psu-epl/Capstones-LID_Tracking/doc/web_interface/Hierarchy_prelim.jpg

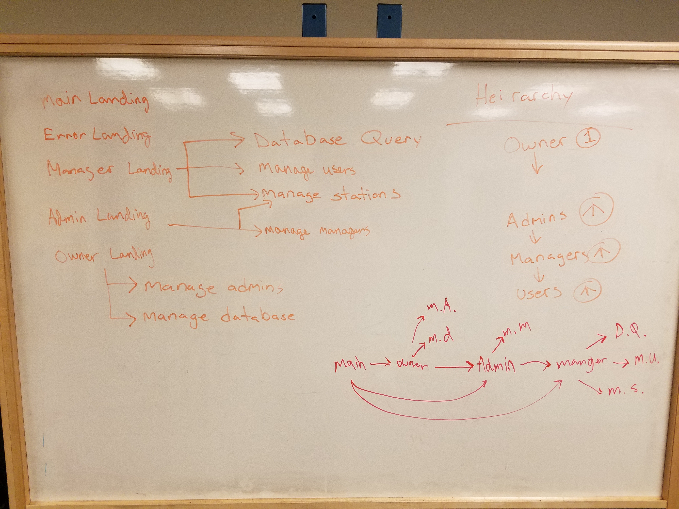
doc/web_interface/Hierarchy_prelim.jpg
