psu-epl/Capstones-LID_Tracking/doc/web_interface/State_Diagram_prelim.jpg

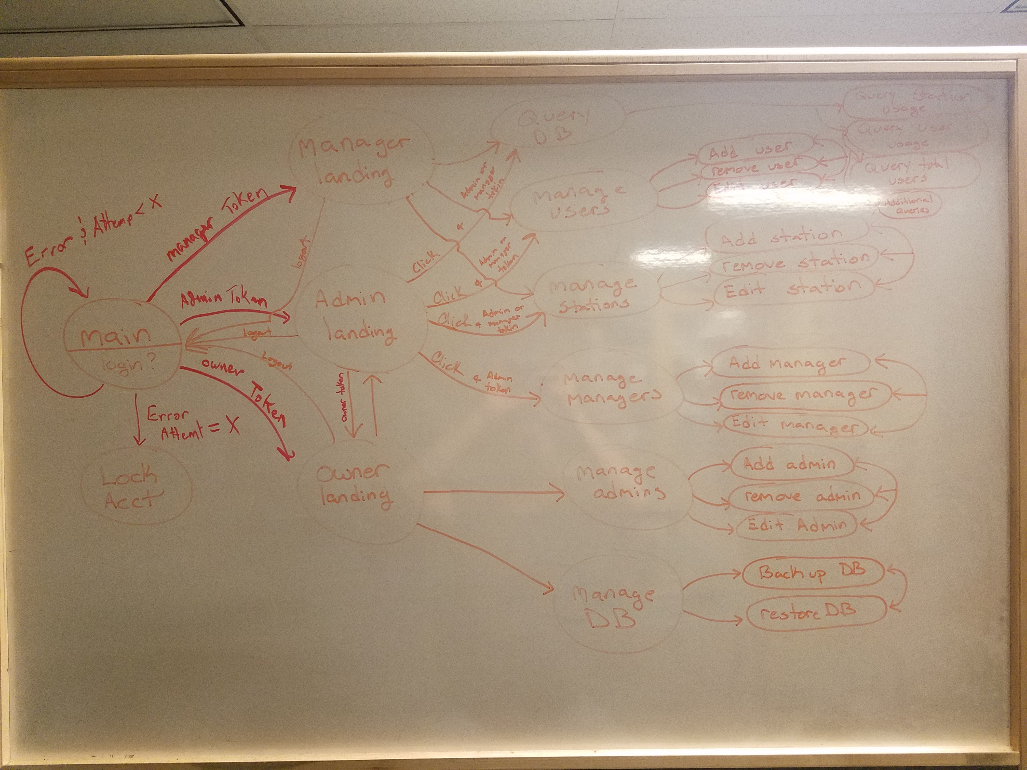
doc/web_interface/State_Diagram_prelim.jpg
